CarlyyR/Multistable_Soft_Robotics/CAD_files/5. Overcurvature/O_0.17_Rn_30_overcurvature.SLDPRT

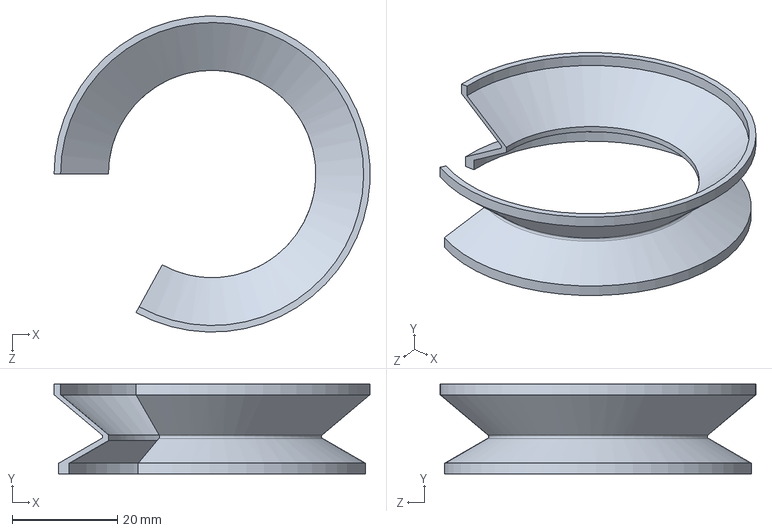
[picture p15: CAD file, 2026-08-18]
CAD_files/5. Overcurvature/O_0.17_Rn_30_overcurvature.SLDPRT
59.9 x 17.0 x 60.0 mm
