CarlyyR/Multistable_Soft_Robotics/CAD_files/6. Silicone_Molds/Mold_part1.SLDPRT

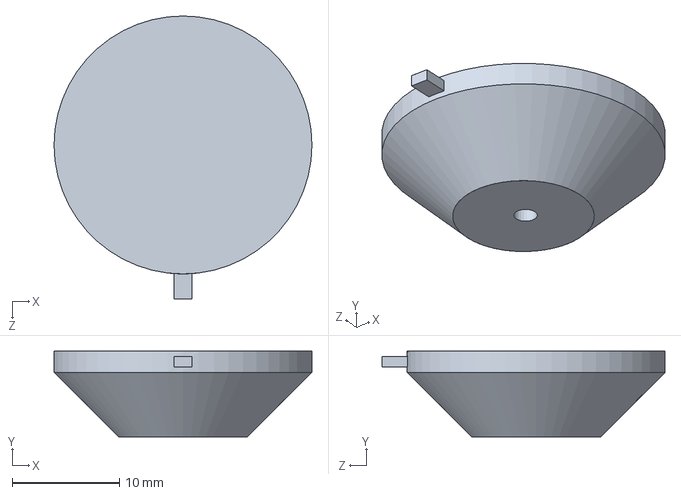
[picture p16: CAD file, 2026-08-18]
CAD_files/6. Silicone_Molds/Mold_part1.SLDPRT
24.0 x 8.00 x 26.3 mm
