CarlyyR/Multistable_Soft_Robotics/CAD_files/4. RCF_Additions/Additions_variations/Collar_decrease.SLDPRT

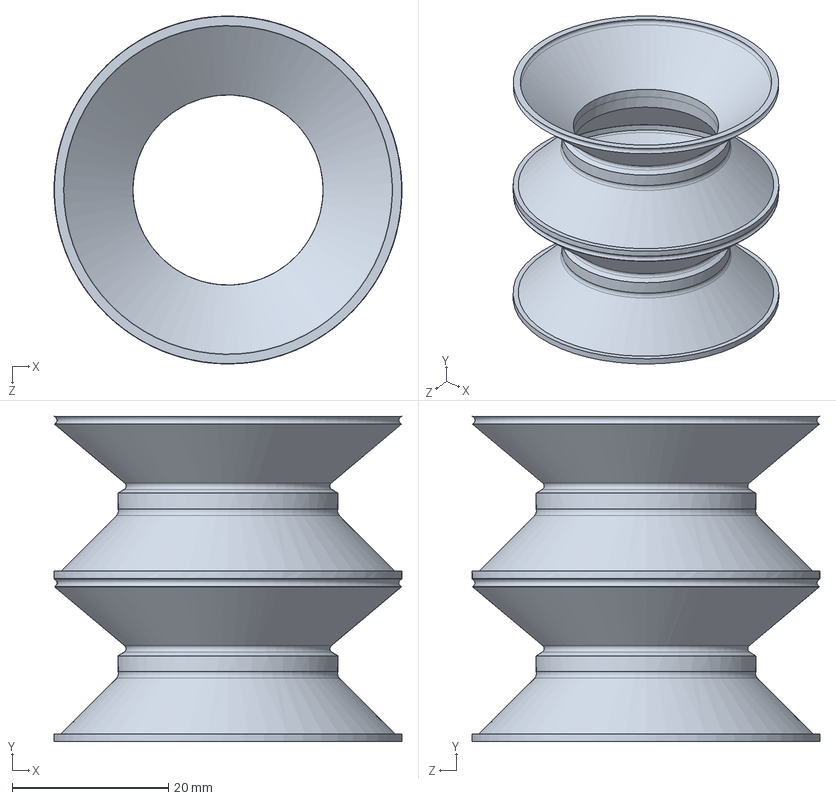
[picture p17: CAD file, 2026-08-18]
CAD_files/4. RCF_Additions/Additions_variations/Collar_decrease.SLDPRT
44.6 x 41.7 x 44.6 mm
