CarlyyR/Multistable_Soft_Robotics/CAD_files/6. Silicone_Molds/Mold_part3.SLDPRT

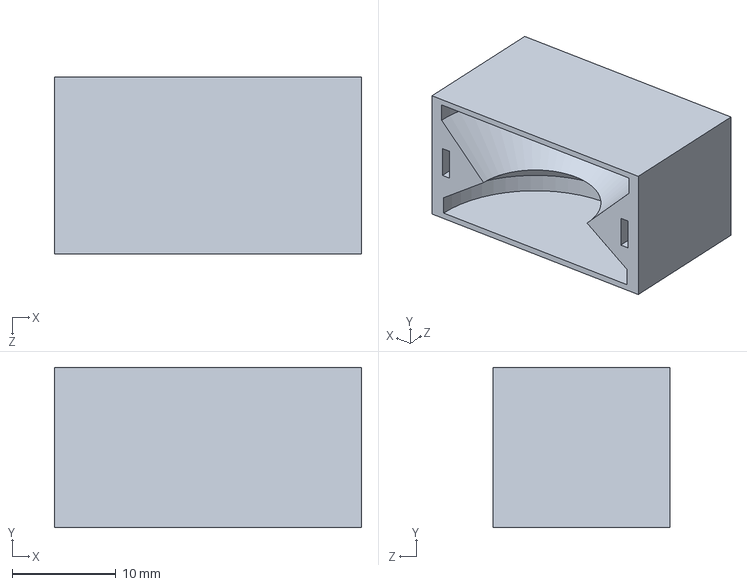
[picture p18: CAD file, 2026-08-18]
CAD_files/6. Silicone_Molds/Mold_part3.SLDPRT
29.5 x 15.4 x 17.0 mm
