CarlyyR/Multistable_Soft_Robotics/CAD_files/1. Finding_Ratios/Iterations/Pop_Tube_Ratios_approx.SLDPRT

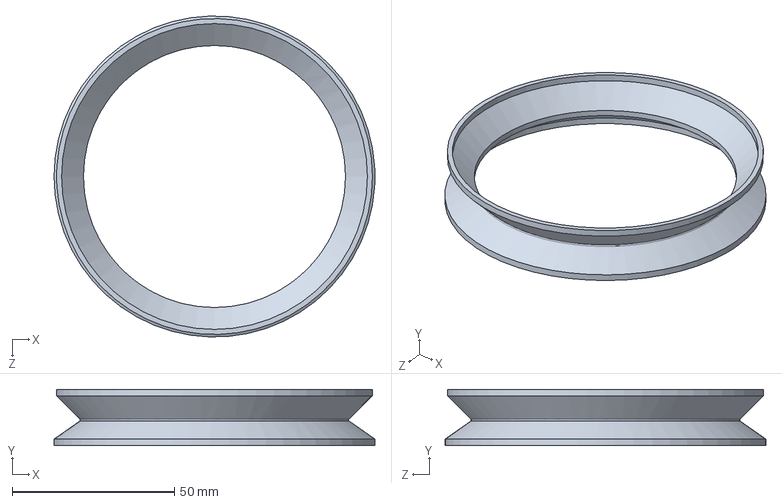
[picture p19: CAD file, 2026-08-18]
CAD_files/1. Finding_Ratios/Iterations/Pop_Tube_Ratios_approx.SLDPRT
98.8 x 17.3 x 98.8 mm
