CarlyyR/Multistable_Soft_Robotics/CAD_files/4. RCF_Additions/Additions_variations/passive_increase.SLDPRT

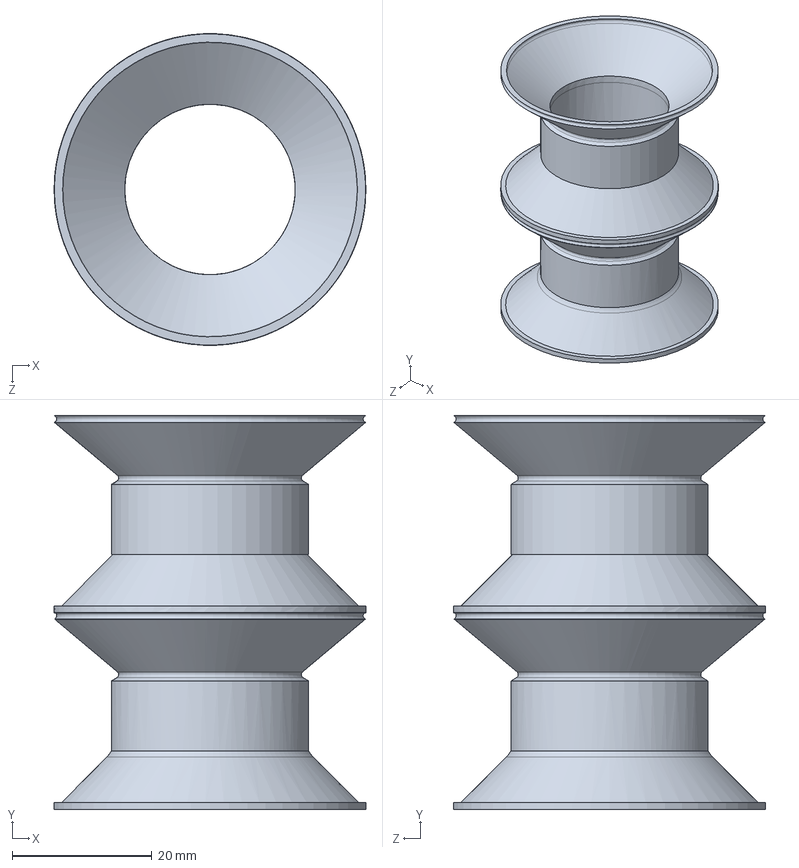
[picture p20: CAD file, 2026-08-18]
CAD_files/4. RCF_Additions/Additions_variations/passive_increase.SLDPRT
44.6 x 56.3 x 44.6 mm
