CarlyyR/Multistable_Soft_Robotics/CAD_files/1. Finding_Ratios/Iterations/exhaggerated_Angles_Passive_thickness.SLDPRT

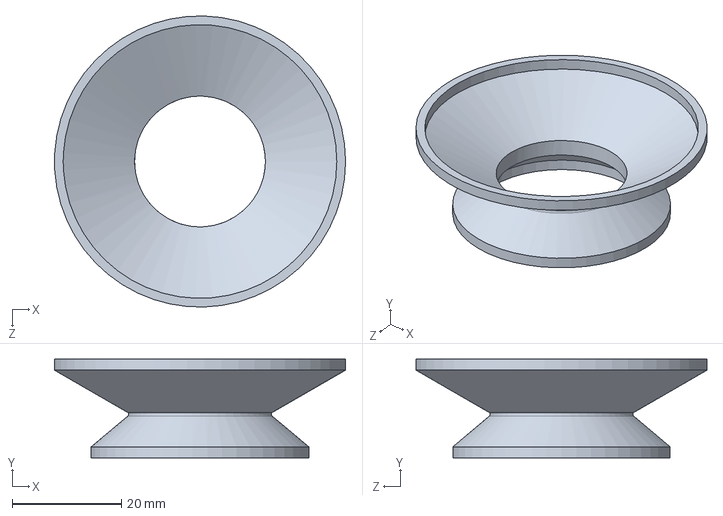
[picture p21: CAD file, 2026-08-18]
CAD_files/1. Finding_Ratios/Iterations/exhaggerated_Angles_Passive_thickness.SLDPRT
53.2 x 18.0 x 53.2 mm
