CarlyyR/Multistable_Soft_Robotics/CAD_files/1. Finding_Ratios/Iterations/final_hinges_on_active.SLDPRT

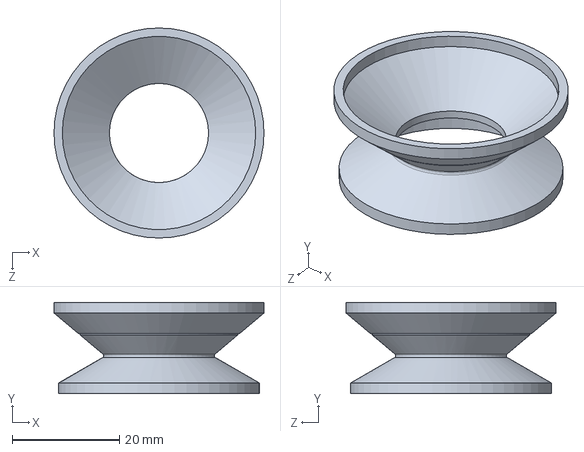
[picture p22: CAD file, 2026-08-18]
CAD_files/1. Finding_Ratios/Iterations/final_hinges_on_active.SLDPRT
39.1 x 17.0 x 39.1 mm
