CarlyyR/Multistable_Soft_Robotics/CAD_files/1. Finding_Ratios/Iterations/Thicker_wider_flipped_h_.SLDPRT

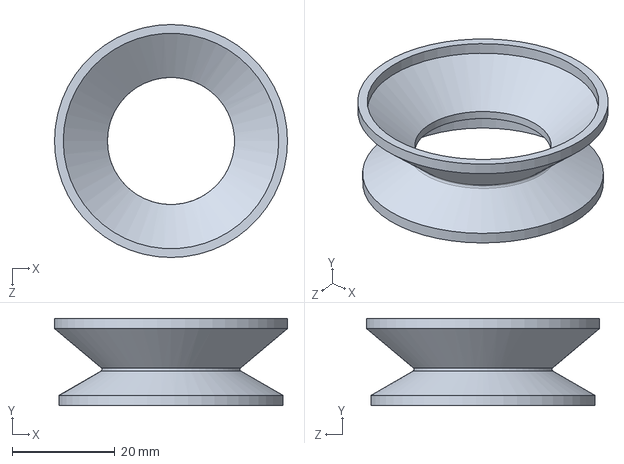
[picture p23: CAD file, 2026-08-18]
CAD_files/1. Finding_Ratios/Iterations/Thicker_wider_flipped_h_.SLDPRT
45.4 x 17.0 x 45.4 mm
