CarlyyR/Multistable_Soft_Robotics/CAD_files/1. Finding_Ratios/Iterations/Final_flipped_angles.SLDPRT

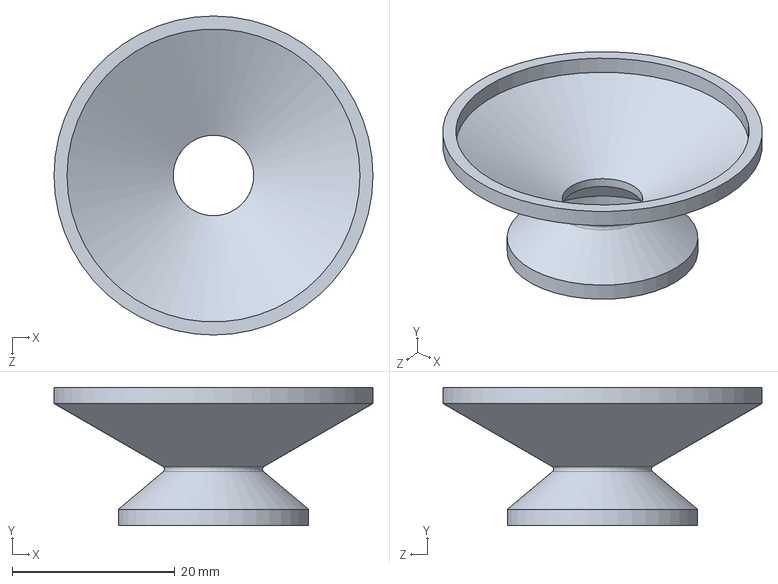
[picture p24: CAD file, 2026-08-18]
CAD_files/1. Finding_Ratios/Iterations/Final_flipped_angles.SLDPRT
39.2 x 17.0 x 39.2 mm
