CarlyyR/Multistable_Soft_Robotics/CAD_files/1. Finding_Ratios/Iterations/Final_angle_decrease.SLDPRT

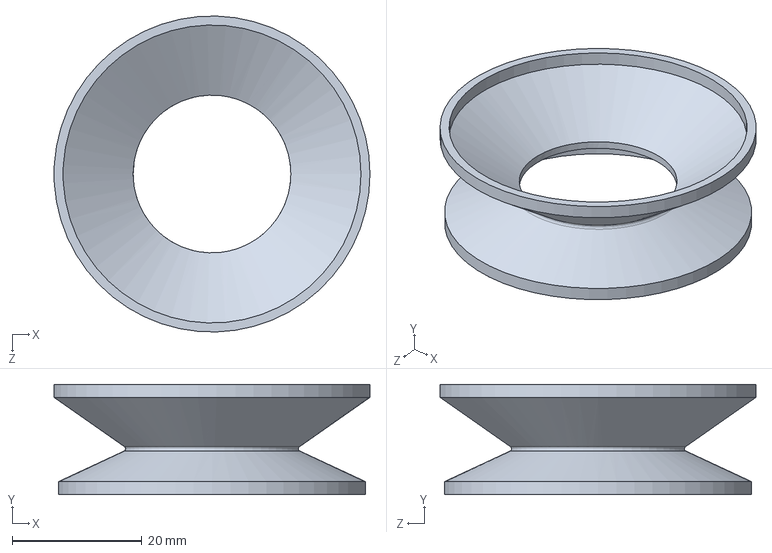
[picture p25: CAD file, 2026-08-18]
CAD_files/1. Finding_Ratios/Iterations/Final_angle_decrease.SLDPRT
48.8 x 17.0 x 48.8 mm
