CarlyyR/Multistable_Soft_Robotics/CAD_files/1. Finding_Ratios/Stacked_Attempts/RCF_stacked_attempt_1.SLDASM

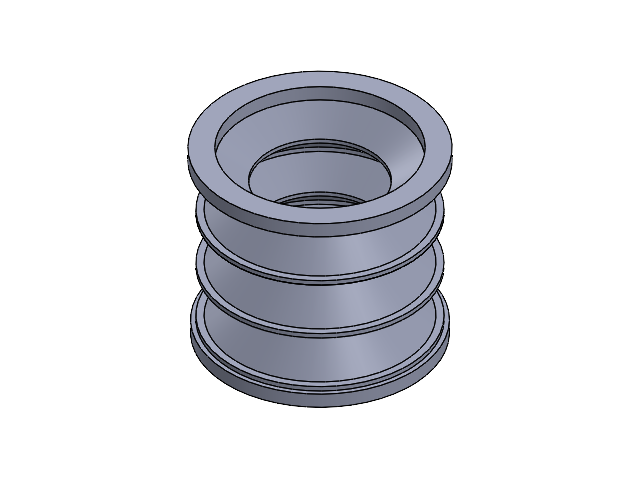
[picture p26: CAD file, 2026-08-18]
CAD_files/1. Finding_Ratios/Stacked_Attempts/RCF_stacked_attempt_1.SLDASM
straw_multistable x 3
Part2^straw_stacked
Part3^straw_stacked
